googlecreativelab/open-nsynth-super/images/ons_pcb_mcu.jpg

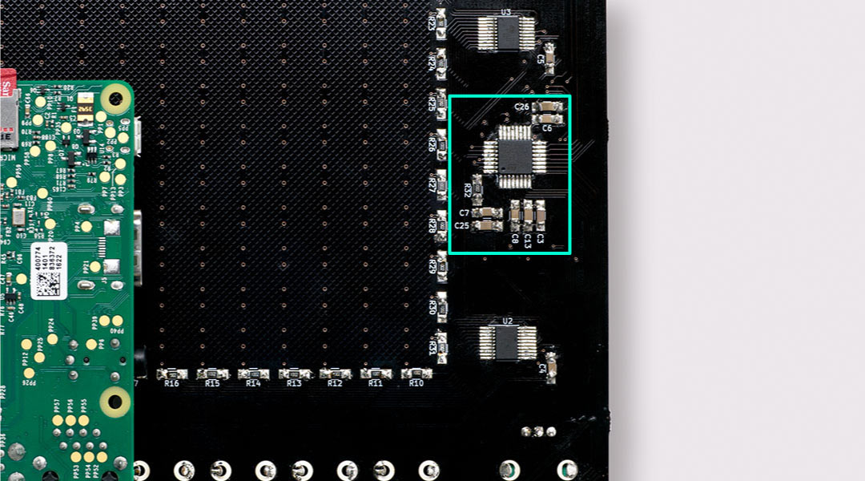
images/ons_pcb_mcu.jpg
