googlecreativelab/open-nsynth-super/pcb_hardware/projects/open-nsynth-super/audio.sch

## KiCad design pcb_hardware/projects/open-nsynth-super/audio.sch (2018-03-20)

Schematic: audio.sch

Parts:
C1, C2: 2.2nF; C_1206_HandSoldering
C9, C10, C11, C12: 0.1uF; C_1206_HandSoldering
C23, C24: 2.2uF; C_1206_HandSoldering
C27, C28, C29, C30: 10uF; C_1206_HandSoldering
R2, R3, R4, R5, R6: 470; R_1206_HandSoldering
R8: 5k6; R_1206_HandSoldering
R9: 10k; R_1206_HandSoldering
U1: PCM512x; TSSOP-28_4.4x9.7mm_Pitch0.65mm
