googlecreativelab/open-nsynth-super/pcb_hardware/projects/open-nsynth-super/mcu.sch

## KiCad design pcb_hardware/projects/open-nsynth-super/mcu.sch (2018-08-10)

Schematic: mcu.sch

Parts:
C3: 0.01uF; C_1206_HandSoldering
C6, C7, C8: 0.1uF; C_1206_HandSoldering
C13: 1uF; C_1206_HandSoldering
C25, C26: 2.2uF; C_1206_HandSoldering
R32: 10k; R_1206_HandSoldering
RV0, RV1, RV2, RV3, RV4, RV5: POT; Potentiometer_Alps_RK09K
SW0, SW1, SW2, SW3: Rotary_Encoder; PEC11R-S
U7: STM32F030K6Tx; LQFP-32_7x7mm_Pitch0.8mm
