googlecreativelab/open-nsynth-super/pcb_hardware/projects/open-nsynth-super/midi.sch

## KiCad design pcb_hardware/projects/open-nsynth-super/midi.sch (2018-03-20)

Schematic: midi.sch

Parts:
D1: DIODE; D_1206
IC1: 6N139; DIP-8_SMD
R1: 220; R_1206_HandSoldering
R7: 470; R_1206_HandSoldering
