googlecreativelab/open-nsynth-super/pcb_hardware/projects/open-nsynth-super/open-nsynth-super.sch

## KiCad design pcb_hardware/projects/open-nsynth-super/open-nsynth-super.sch (2018-08-10)

Schematic: open-nsynth-super.sch

Parts:
J1: Raspberry_Pi_2_3; RPi
J2: DIN-5_180degree; MIDI
J3: OLED13; oled13
J4: USB_OTG; USB_Micro-B
J9: Audio-Jack-3; KLBR_4
