googlecreativelab/open-nsynth-super/pcb_hardware/projects/open-nsynth-super/power.sch

## KiCad design pcb_hardware/projects/open-nsynth-super/power.sch (2018-03-20)

Schematic: power.sch

Parts:
C14, C15, C16, C17, C18, C19, C20, C21, C22: 1uF; C_1206_HandSoldering
U4, U5, U6: TPS73133; SOT-23-5
