googlecreativelab/open-nsynth-super/pcb_hardware/projects/open-nsynth-super/touch.sch

## KiCad design pcb_hardware/projects/open-nsynth-super/touch.sch (2018-03-20)

Schematic: touch.sch

Parts:
C4, C5: 0.1uF; C_1206_HandSoldering
R10, R11, R12, R13, R14, R15, R16, R17, R18, R19, R20, R21, R22, R23, R24, R25, R26, R27, R28, R29, R30, R31: 10k; R_1206_HandSoldering
TC1, TC2, TC3, TC4, TC5, TC6, TC7, TC8, TC9, TC10, TC11, TC12, TC13, TC14, TC15, TC16, TC17, TC18, TC19, TC20, TC21, TC22, TC23, TC24, TC25, TC26, TC27, TC28, TC29, TC30, TC31, TC32, TC33, TC34, TC35, TC36, TC37, TC38, TC39, TC40, TC41, TC42, TC43, TC44, TC45, TC46, TC47, TC48, TC49, TC50, TC51, TC52, TC53, TC54, TC55, TC56, TC57, TC58, TC59, TC60, TC61, TC62, TC63, TC64, TC65, TC66, TC67, TC68, TC69, TC70, TC71, TC72, TC73, TC74, TC75, TC76, TC77, TC78, TC79, TC80, TC81, TC82, TC83, TC84, TC85, TC86, TC87, TC88, TC89, TC90, TC91, TC92, TC93, TC94, TC95, TC96, TC97, TC98, TC99, TC100, TC101, TC102, TC103, TC104, TC105, TC106, TC107, TC108, TC109, TC110, TC111, TC112, TC113, TC114, TC115, TC116, TC117, TC118, TC119, TC120, TC121: touch; touch_cell
U2, U3: AT42QT2120; TSSOP-20_4.4x6.5mm_Pitch0.65mm
